HSMinches/RadHard/Electronics/Ansys_thermal/temp_analysis.png

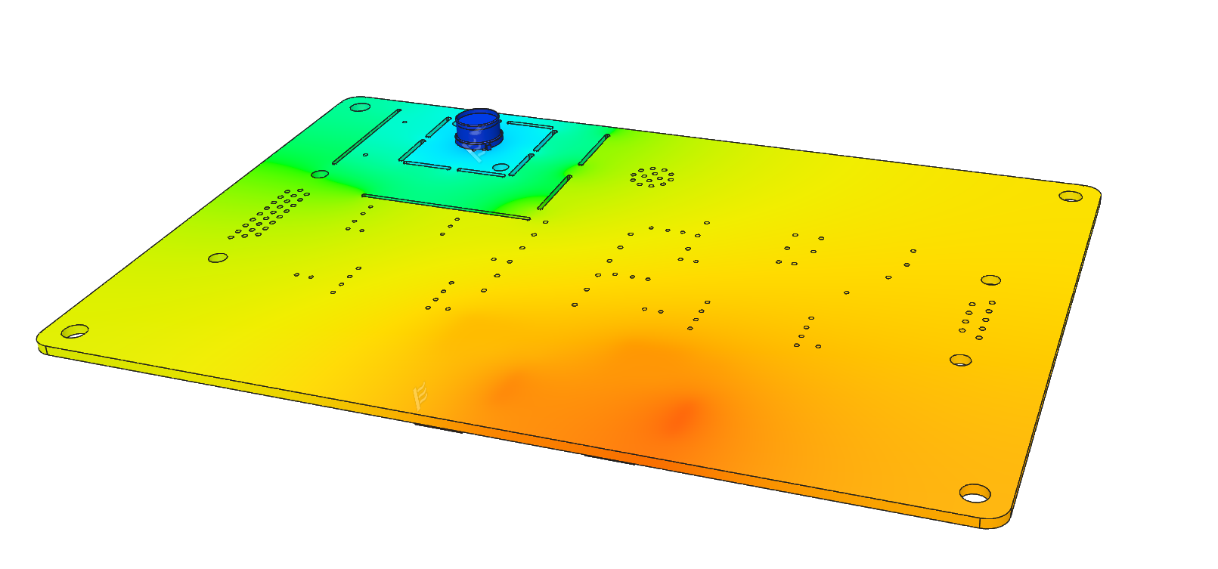
Electronics/Ansys_thermal/temp_analysis.png
