HSMinches/RadHard/Electronics/Ansys_thermal/temp_analysis_bottom.png

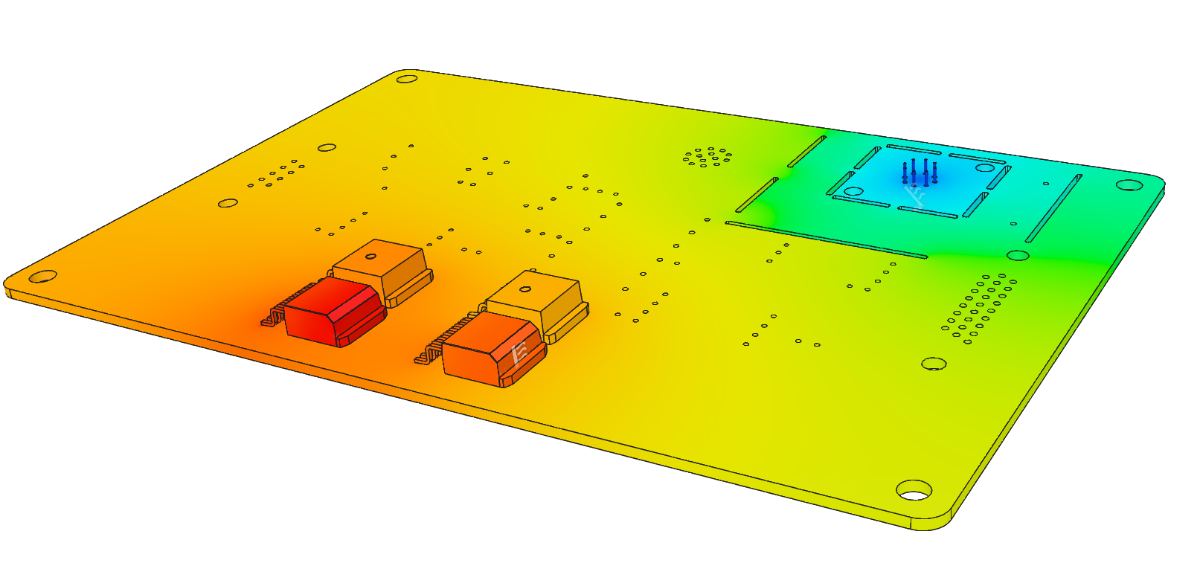
Electronics/Ansys_thermal/temp_analysis_bottom.png
