HSMinches/RadHard/InitialConcept/Initial concept_enclosure.png

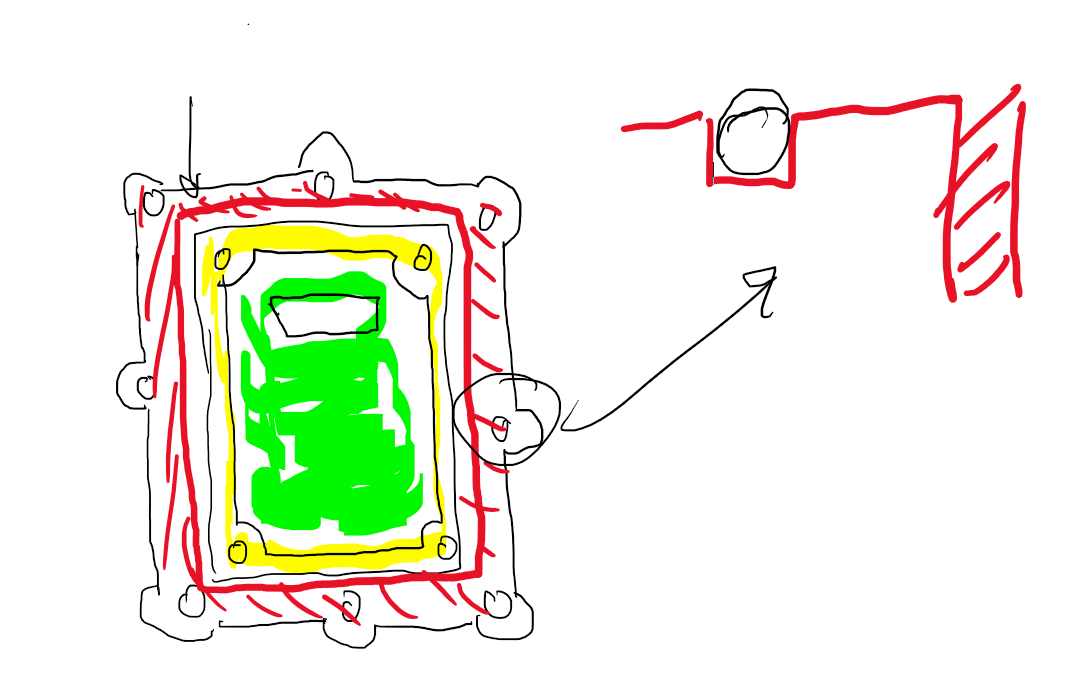
InitialConcept/Initial concept_enclosure.png
