HSMinches/RadHard/InitialConcept/Initial concept_high level block .png

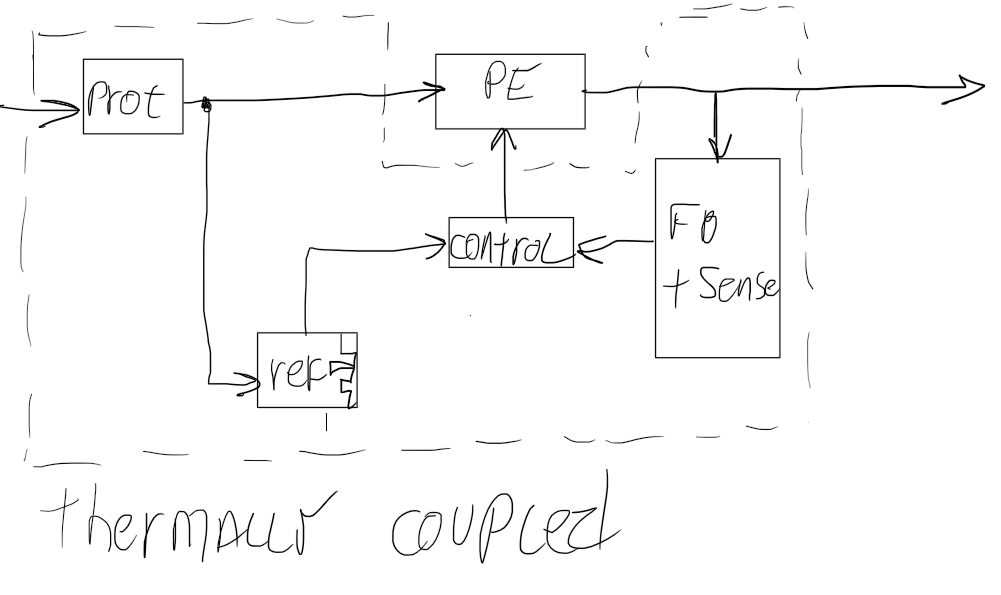
InitialConcept/Initial concept_high level block .png
