HSMinches/RadHard/Enclosure/Montagem1-2.jpg

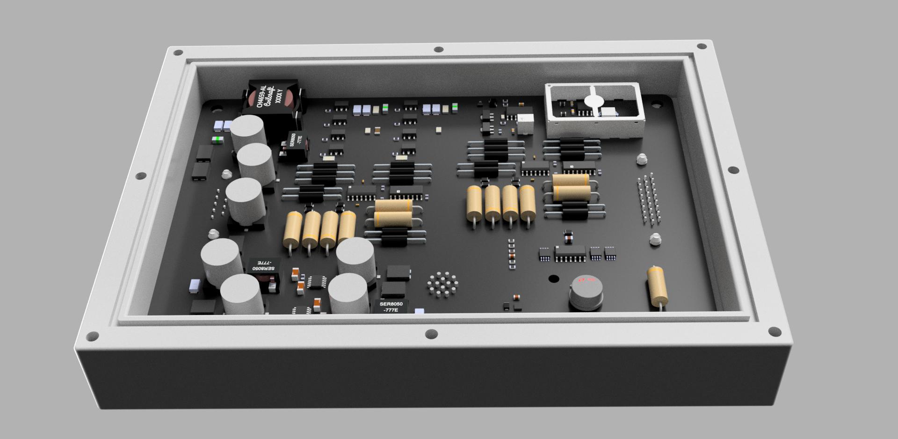
Enclosure/Montagem1-2.jpg
