HSMinches/RadHard/Enclosure/Montagem1-3.jpg

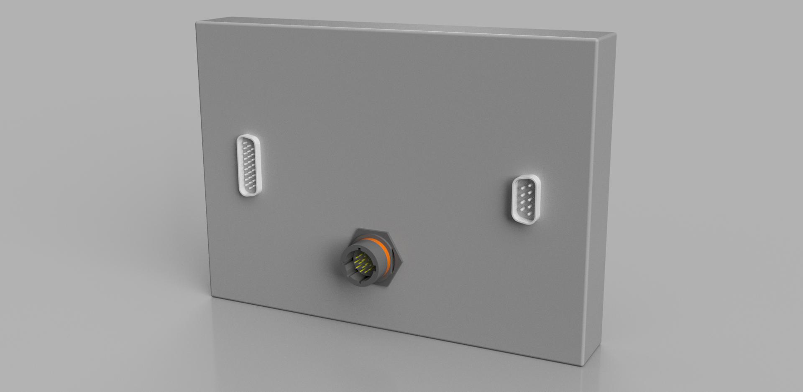
Enclosure/Montagem1-3.jpg
