HSMinches/RadHard/Enclosure/Montagem1.jpg

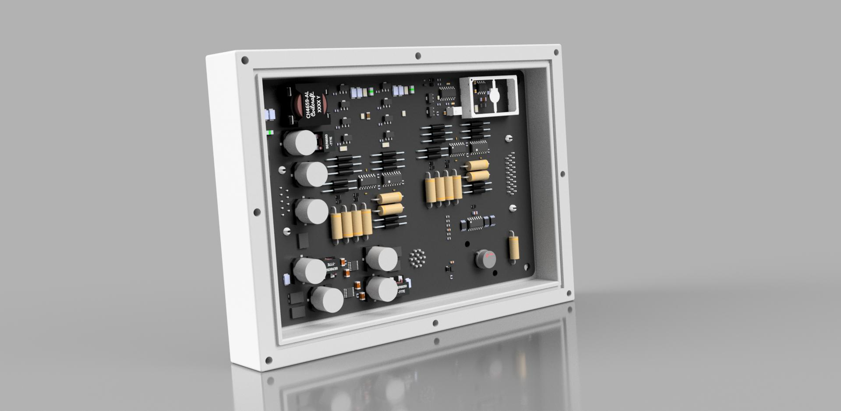
Enclosure/Montagem1.jpg
