HSMinches/RadHard/Electronics/AltiumProject/Rad_hard_git/PDNAnalyzer_Output/radhard/Sim_OutputCurrent/Results/vias.csv

x | y | layer1 | layer2 | voltage1 | voltage2 | current
1088.08 | 1213.25 | TOP_LAYER | INT1__GND_ | 0.00272075 | 0.00272075 | -0
1088.08 | 1213.25 | INT1__GND_ | INT2__SIGN_ | 0.00272075 | 0.00272075 | -6.09483e-16
1088.08 | 1213.25 | INT2__SIGN_ | INT3__SIGN_ | 0.00272075 | 0.00272075 | -0
1088.08 | 1213.25 | INT3__SIGN_ | INT4__PWR_ | 0.00272075 | 0.00272075 | -6.09483e-16
1088.08 | 1213.25 | INT4__PWR_ | BOTTOM_LAYER | 0.00272075 | 0.00272075 | -0
1088.08 | 1262.47 | TOP_LAYER | INT1__GND_ | 0.0027211 | 0.0027211 | -0
1088.08 | 1262.47 | INT1__GND_ | INT2__SIGN_ | 0.0027211 | 0.0027211 | -1.82845e-15
1088.08 | 1262.47 | INT2__SIGN_ | INT3__SIGN_ | 0.0027211 | 0.0027211 | -2.25899e-15
1088.08 | 1262.47 | INT3__SIGN_ | INT4__PWR_ | 0.0027211 | 0.0027211 | -6.09483e-16
1088.08 | 1262.47 | INT4__PWR_ | BOTTOM_LAYER | 0.0027211 | 0.0027211 | -0
1088.08 | 1311.68 | TOP_LAYER | INT1__GND_ | 0.00272134 | 0.00272134 | -0
1088.08 | 1311.68 | INT1__GND_ | INT2__SIGN_ | 0.00272134 | 0.00272134 | -6.09483e-16
1088.08 | 1311.68 | INT2__SIGN_ | INT3__SIGN_ | 0.00272134 | 0.00272134 | -0
1088.08 | 1311.68 | INT3__SIGN_ | INT4__PWR_ | 0.00272134 | 0.00272134 | -6.09483e-16
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
